Evil-Ender/FG927/src/num48_24.h

uint8_t num48_240[1152]={
B00111111,B11111111,B11110011,
B01111111,B11111111,B11110111,
B11111111,B11111111,B11110111,
B01111111,B11111111,B11100111,
B00001111,B11111111,B11101111,
B11100000,B00000000,B00001111,
B11111000,B00000000,B00001111,
B11111000,B00000000,B00001111,
B11111000,B00000000,B00001111,
B11111000,B00000000,B00001111,
B11111000,B00000000,B00001111,
B11111000,B00000000,B00001111,
B11111000,B00000000,B00001111,
B11111000,B00000000,B00001111,
B11111000,B00000000,B00001111,
B11111000,B00000000,B00001111,
B11111000,B00000000,B00001111,
B11111000,B00000000,B00001111,
B11111000,B00000000,B00001111,
B11111000,B00000000,B00000111,
B11110000,B00000000,B00000111,
B11100000,B00000000,B00000011,
B01000000,B00000000,B00000001,
B00000000,B00000000,B00000000,
B00000000,B00000000,B00000000,
B01000000,B00000000,B00000001,
B11100000,B00000000,B00000011,
B11110000,B00000000,B00000111,
B11111000,B00000000,B00000111,
B11111000,B00000000,B00001111,
B11111000,B00000000,B00001111,
B11111000,B00000000,B00001111,
B11111000,B00000000,B00001111,
B11111000,B00000000,B00001111,
B11111000,B00000000,B00001111,
B11111000,B00000000,B00001111,
B11111000,B00000000,B00001111,
B11111000,B00000000,B00001111,
B11111000,B00000000,B00001111,
B11111000,B00000000,B00001111,
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
};

uint8_t num48_241[1152]={
B00000000,B00000000,B00000010,
B00000000,B00000000,B00000111,
B00000000,B00000000,B00000111,
B00000000,B00000000,B00000111,
B00000000,B00000000,B00001111,
B00000000,B00000000,B00001111,
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
B00000000,B00000000,B00001111,
B00000000,B00000000,B00001111,
B00000000,B00000000,B00001111,
B00000000,B00000000,B00001111,
B00000000,B00000000,B00001111,
B00000000,B00000000,B00001111,
B00000000,B00000000,B00001111,
B00000000,B00000000,B00001111,
B00000000,B00000000,B00001111,
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
};
