Evil-Ender/FG927/src/num96_48.h

uint8_t num96_480[4608]={
B00001111,B11111111,B11111111,B11111111,B11111111,B00100000,
B00011111,B11111111,B11111111,B11111111,B11111111,B00111000,
B00111111,B11111111,B11111111,B11111111,B11111110,B00111100,
B01111111,B11111111,B11111111,B11111111,B11111110,B01111110,
B01111111,B11111111,B11111111,B11111111,B11111110,B01111110,
B11111111,B11111111,B11111111,B11111111,B11111100,B01111111,
B11111111,B11111111,B11111111,B11111111,B11111100,B11111111,
B01111111,B11111111,B11111111,B11111111,B11111100,B11111111,
B00001111,B11111111,B11111111,B11111111,B11111000,B11111111,
B00000011,B11111111,B11111111,B11111111,B11111001,B11111111,
B11000000,B11111111,B11111111,B11111111,B11111001,B11111111,
B11110000,B00000000,B00000000,B00000000,B00000001,B11111111,
B11111100,B00000000,B00000000,B00000000,B00000001,B11111111,
B11111111,B10000000,B00000000,B00000000,B00000001,B11111111,
B11111111,B10000000,B00000000,B00000000,B00000001,B11111111,
B11111111,B10000000,B00000000,B00000000,B00000001,B11111111,
B11111111,B10000000,B00000000,B00000000,B00000001,B11111111,
B11111111,B10000000,B00000000,B00000000,B00000001,B11111111,
B11111111,B10000000,B00000000,B00000000,B00000001,B11111111,
B11111111,B10000000,B00000000,B00000000,B00000001,B11111111,
B11111111,B10000000,B00000000,B00000000,B00000001,B11111111,
B11111111,B10000000,B00000000,B00000000,B00000001,B11111111,
B11111111,B10000000,B00000000,B00000000,B00000001,B11111111,
B11111111,B10000000,B00000000,B00000000,B00000001,B11111111,
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
B00000000,B00000000,B00000000,
B00000000,B00000000,B00000000,
B00000000,B00000000,B00000000,
B00000000,B00000000,B00000000,
B00000000,B00000000,B00000000,
B00000000,B00000000,B00000000,
B00000000,B00000000,B00000000,
B00000000,B00000000,B00000000,
B00000000,B00000000,B00000000,
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
};
