Evil-Ender/FG927/src/MS5xxx.h

/*
    MS5xxx.h - Library for accessing MS5xxx sensors via I2C
    Copyright (c) 2012 Roman Schmitz

    This file is part of arduino-ms5xxx.

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
*/

#if defined(ESP32)
  // 对ESP32特有的定义
  
#elif defined(ARDUINO_AVR_UNO)
  // 对Arduino Uno特有的定义
  #define Wire1 Wire
#elif defined(ARDUINO_AVR_MEGA2560)
  // 对Arduino Mega 2560特有的定义
  #define Wire1 Wire
#else
  #error "This library only supports ESP32 and AVR-based Arduino boards."
#endif

#ifndef MS5xxx_h
#define MS5xxx_h

#include "Arduino.h"
#include <Wire.h>

// typical I2C-Address of chip
#define I2C_MS5607 0x76
#define I2C_MS5611 0x77

// I2C commands of chip
#define MS5xxx_CMD_RESET 0x1E    // perform reset
#define MS5xxx_CMD_ADC_READ 0x00 // initiate read sequence
#define MS5xxx_CMD_ADC_CONV 0x40 // start conversion
#define MS5xxx_CMD_ADC_D1 0x00   // read ADC 1
#define MS5xxx_CMD_ADC_D2 0x10   // read ADC 2
#define MS5xxx_CMD_ADC_256 0x00  // set ADC oversampling ratio to 256
#define MS5xxx_CMD_ADC_512 0x02  // set ADC oversampling ratio to 512
#define MS5xxx_CMD_ADC_1024 0x04 // set ADC oversampling ratio to 1024
#define MS5xxx_CMD_ADC_2048 0x06 // set ADC oversampling ratio to 2048
#define MS5xxx_CMD_ADC_4096 0x08 // set ADC oversampling ratio to 4096
#define MS5xxx_CMD_PROM_RD 0xA0  // initiate readout of PROM registers

class MS5xxx
{
protected:
  unsigned int C[8];
  double P;
  double TEMP;
  char i2caddr;
  TwoWire *_Wire;
  
  double dT;
  double OFF;
  double SENS;
  double T2 = 0., OFF2 = 0., SENS2 = 0.;

  unsigned char send_cmd(unsigned char aCMD);
  unsigned long read_adc(unsigned char aCMD);

public:
  MS5xxx(TwoWire *aWire);
  void setI2Caddr(char aAddr);
  byte connect();

  void ReadProm();
  void Readout();

  unsigned int Calc_CRC4(unsigned char poly = 0x30);
  unsigned int Read_CRC4();
  unsigned char CRCcodeTest();

  unsigned int Read_C(unsigned int index);

  double GetTemp();
  double GetPres();
  void Readout_once();
  double get_P();
  void start_mesure(byte D1_OSR);
  void set_wire();
  void set_wire1();
  void begin_wire();
  void begin_wire1();
};

#endif
