Evil-Ender/FG927/src/batt.h

uint8_t batt0[312]={
B11111111,B11111111,B11111100,
B11111111,B11111111,B11111100,
B11111111,B11111001,B11011100,
B11000000,B00000000,B00011110,
B11000000,B00000000,B10011110,
B11000000,B00000000,B01111110,
B11000000,B00000000,B10011110,
B11000000,B00000000,B00011110,
B11000000,B00000000,B00011110,
B11000000,B00000000,B00011110,
B11100000,B00000000,B00011100,
B11111111,B11111111,B11111100,
B11111111,B11111111,B11111100
};

uint8_t batt1[312]={
B11111111,B11111111,B11111100,
B11111111,B11111111,B11111100,
B11010111,B11111101,B11011100,
B11011100,B00000000,B00011110,
B11011100,B00000000,B00011110,
B11011100,B00000000,B00011110,
B11011100,B00000000,B00011110,
B11011100,B00000000,B00011110,
B11011100,B00000000,B00011110,
B11011100,B00000000,B00011110,
B11000000,B00000000,B00111100,
B11111111,B11111111,B11111100,
B11111111,B11111111,B11111100
};

uint8_t batt2[312]={
B11111111,B11111111,B11111100,
B11111111,B11111111,B11111100,
B11010111,B11111101,B11011100,
B11011101,B11000000,B00011110,
B11011101,B11000000,B00011110,
B11011101,B11000000,B00011110,
B11011101,B11000000,B00011110,
B11011101,B11000000,B00011110,
B11011101,B11000000,B00011110,
B11011101,B11000000,B00011110,
B11000000,B00000000,B00111100,
B11111111,B11111111,B11111100,
B11111111,B11111111,B11111100
};

uint8_t batt3[312]={
B11111111,B11111111,B11111100,
B11111111,B11111111,B11111100,
B11010111,B11111001,B11011100,
B11011101,B11011100,B00011110,
B11011101,B11011100,B00011110,
B11011101,B11011100,B00011110,
B11011101,B11011100,B00011110,
B11011101,B11011100,B00011110,
B11011101,B11011100,B00011110,
B11011101,B11011100,B00011110,
B11000000,B00000000,B00111100,
B11111111,B11111111,B11111100,
B11111111,B11111111,B11111100
};

uint8_t batt4[312]={
B11111111,B11111111,B11111100,
B11111111,B11111111,B11111100,
B11010111,B11111001,B11011100,
B11011101,B11011101,B11011110,
B11011101,B11011101,B11011110,
B11011101,B11011101,B11011110,
B11011101,B11011101,B11011110,
B11011101,B11011101,B11011110,
B11011101,B11011101,B11011110,
B11011101,B11011101,B11011110,
B11000000,B00000000,B00111100,
B11111111,B11111111,B11111100,
B11111111,B11111111,B11111100
};

uint8_t batt5[120]={
B00001000,
B00011000,
B00011000,
B00111000,
B00111000,
B01111111,
B01111111,
B11111111,
B11111110,
B11111110,
B00011100,
B00011100,
B00011000,
B00011000,
B00010000
};
