Evil-Ender/FG927/src/ionic.h

uint8_t ionicx16_0[256]={
B00000000,B00000110,
B00000000,B00001111,
B00000000,B00011111,
B00000000,B00111110,
B00000111,B01111100,
B00001111,B10111000,
B00001111,B11110000,
B00000111,B11101111,
B00000111,B11111111,
B00001111,B11111110,
B00011101,B11111100,
B00111110,B11111000,
B01111101,B11111100,
B11111001,B11101110,
B11110001,B11000110,
B01100001,B10000000
};
